homebrew8088/8088-PC-Compatible/Kicad/Other PCBs/ISA_BB/ISA_BB.kicad_pcb

## KiCad design Kicad/Other PCBs/ISA_BB/ISA_BB.kicad_pcb (2023-02-14)

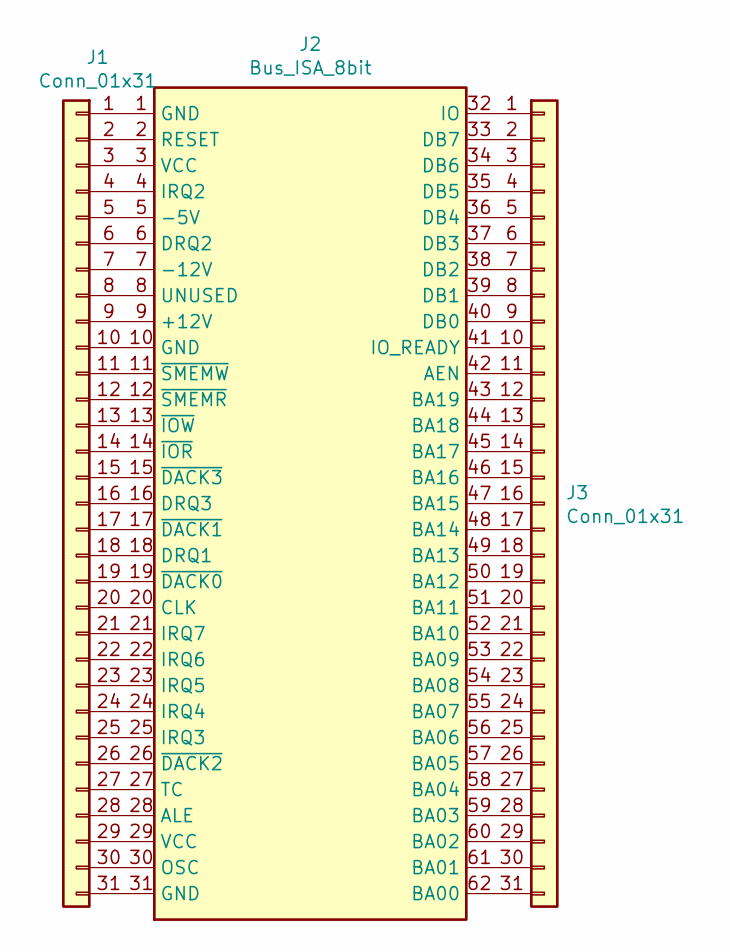
[picture p30: schematic ISA_BB.sch]

Parts:
J1, J3: Conn_01x31; PinHeader_1x31_P2.54mm_Vertical
J2: Bus_ISA_8bit; 8-bit-ISA

Connections:
unnamed: J1.1, J2.1 (GND)
unnamed: J1.2, J2.2 (RESET)
unnamed: J1.3, J2.3 (VCC)
unnamed: J1.4, J2.4 (IRQ2)
unnamed: J1.5, J2.5 (-5V)
unnamed: J1.6, J2.6 (DRQ2)
unnamed: J1.7, J2.7 (-12V)
unnamed: J1.8, J2.8 (UNUSED)
unnamed: J1.9, J2.9 (+12V)
unnamed: J1.10, J2.10 (GND)
unnamed: J1.11, J2.11 (~SMEMW)
unnamed: J1.12, J2.12 (~SMEMR)
unnamed: J1.13, J2.13 (~IOW)
unnamed: J1.14, J2.14 (~IOR)
unnamed: J1.15, J2.15 (~DACK3)
unnamed: J1.16, J2.16 (DRQ3)
unnamed: J1.17, J2.17 (~DACK1)
unnamed: J1.18, J2.18 (DRQ1)
unnamed: J1.19, J2.19 (~DACK0)
unnamed: J1.20, J2.20 (CLK)
unnamed: J1.21, J2.21 (IRQ7)
unnamed: J1.22, J2.22 (IRQ6)
unnamed: J1.23, J2.23 (IRQ5)
unnamed: J1.24, J2.24 (IRQ4)
unnamed: J1.25, J2.25 (IRQ3)
unnamed: J1.26, J2.26 (~DACK2)
unnamed: J1.27, J2.27 (TC)
unnamed: J1.28, J2.28 (ALE)
unnamed: J1.29, J2.29 (VCC)
unnamed: J1.30, J2.30 (OSC)
unnamed: J1.31, J2.31 (GND)
unnamed: J2.32 (IO), J3.1
unnamed: J2.33 (DB7), J3.2
unnamed: J2.34 (DB6), J3.3
unnamed: J2.35 (DB5), J3.4
unnamed: J2.36 (DB4), J3.5
unnamed: J2.37 (DB3), J3.6
unnamed: J2.38 (DB2), J3.7
unnamed: J2.39 (DB1), J3.8
unnamed: J2.40 (DB0), J3.9
unnamed: J2.41 (IO_READY), J3.10
unnamed: J2.42 (AEN), J3.11
unnamed: J2.43 (BA19), J3.12
unnamed: J2.44 (BA18), J3.13
unnamed: J2.45 (BA17), J3.14
unnamed: J2.46 (BA16), J3.15
unnamed: J2.47 (BA15), J3.16
unnamed: J2.48 (BA14), J3.17
unnamed: J2.49 (BA13), J3.18
unnamed: J2.50 (BA12), J3.19
unnamed: J2.51 (BA11), J3.20
unnamed: J2.52 (BA10), J3.21
unnamed: J2.53 (BA09), J3.22
unnamed: J2.54 (BA08), J3.23
unnamed: J2.55 (BA07), J3.24
unnamed: J2.56 (BA06), J3.25
unnamed: J2.57 (BA05), J3.26
unnamed: J2.58 (BA04), J3.27
unnamed: J2.59 (BA03), J3.28
unnamed: J2.60 (BA02), J3.29
unnamed: J2.61 (BA01), J3.30
unnamed: J2.62 (BA00), J3.31

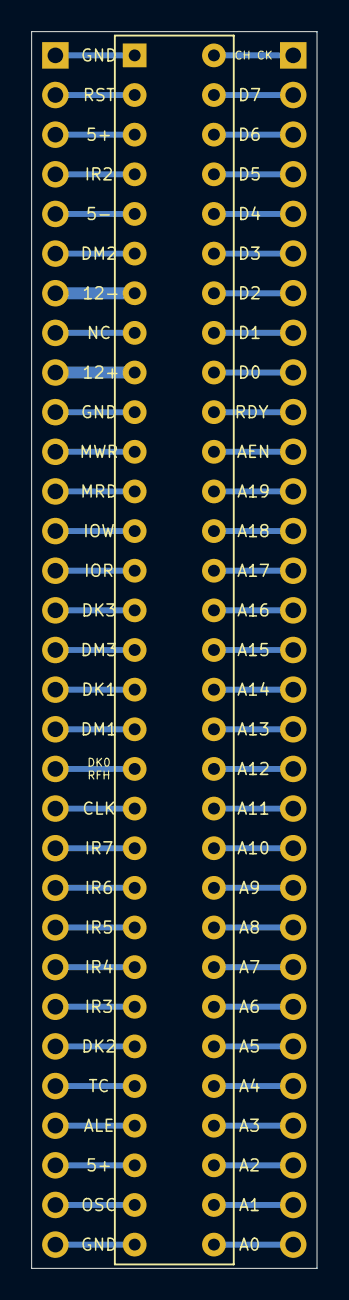
[picture p31: board ISA_BB.kicad_pcb from above]

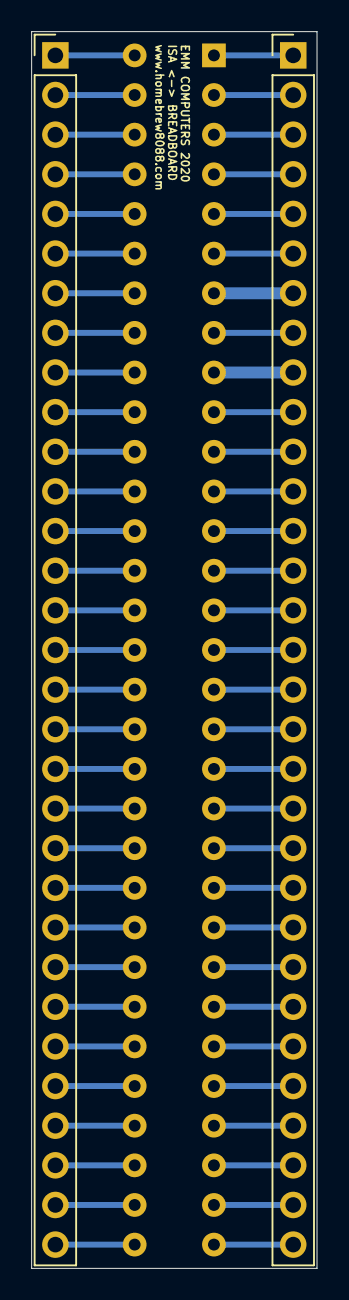
[picture p32: board ISA_BB.kicad_pcb from below]

Board: 2 copper layers, 18.3 x 79.2 mm, 3 parts (2 on the bottom side), 62 nets.
