homebrew8088/8088-PC-Compatible/Kicad/Other PCBs/512K ISA/512k.kicad_pcb

## KiCad design Kicad/Other PCBs/512K ISA/512k.kicad_pcb (2022-01-28)

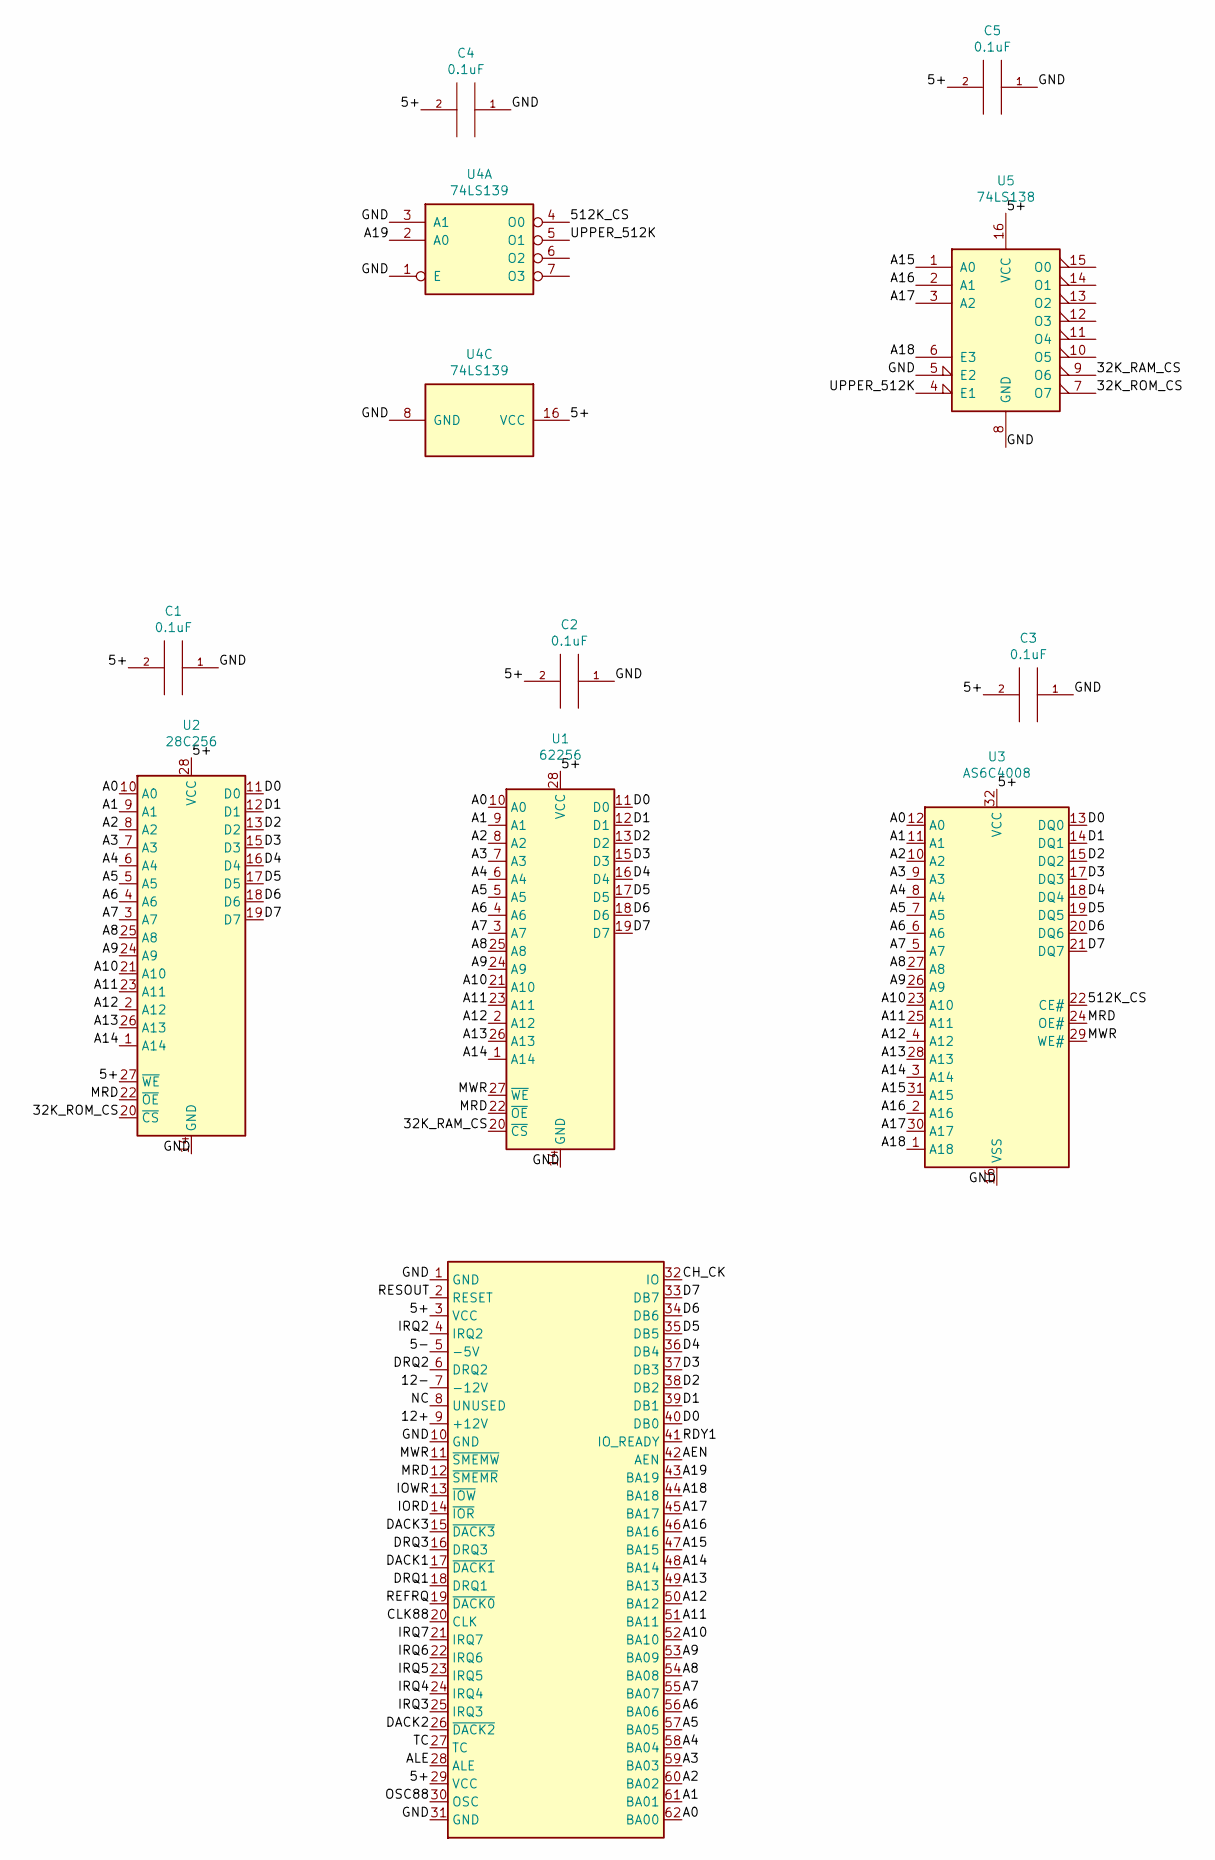
[picture p33: schematic 512k.sch]

Parts:
C1, C2, C3, C4, C5: 0.1uF; C_Disc_D4.3mm_W1.9mm_P5.00mm
J9: Bus_ISA_8bit; BUS_8_BIT
U1: 62256; DIP-28_W15.24mm
U2: 28C256; DIP_Socket-28_W11.9_W12.7_W15.24_W17.78_W18.5_3M_228-1277-0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
U3: AS6C4008; DIP-32_W15.24mm
U4: 74LS139; DIP-16_W7.62mm
U5: 74LS138; DIP-16_W7.62mm

Connections:
/5+: C1.2, C2.2, C3.2, C4.2, C5.2, J9.3 (VCC), J9.29 (VCC), U1.28 (VCC), U2.27 (~WE), U2.28 (VCC), U3.32 (VCC), U4.16 (VCC), U5.16 (VCC)
/5-: J9.5 (-5V)
/12+: J9.9 (+12V)
/12-: J9.7 (-12V)
/32K_RAM_CS: U1.20 (~CS), U5.9 (O6)
/32K_ROM_CS: U2.20 (~CS), U5.7 (O7)
/512K_CS: U3.22 (CE#), U4.4 (O0)
/A0: J9.62 (BA00), U1.10 (A0), U2.10 (A0), U3.12 (A0)
/A1: J9.61 (BA01), U1.9 (A1), U2.9 (A1), U3.11 (A1)
/A2: J9.60 (BA02), U1.8 (A2), U2.8 (A2), U3.10 (A2)
/A3: J9.59 (BA03), U1.7 (A3), U2.7 (A3), U3.9 (A3)
/A4: J9.58 (BA04), U1.6 (A4), U2.6 (A4), U3.8 (A4)
/A5: J9.57 (BA05), U1.5 (A5), U2.5 (A5), U3.7 (A5)
/A6: J9.56 (BA06), U1.4 (A6), U2.4 (A6), U3.6 (A6)
/A7: J9.55 (BA07), U1.3 (A7), U2.3 (A7), U3.5 (A7)
/A8: J9.54 (BA08), U1.25 (A8), U2.25 (A8), U3.27 (A8)
/A9: J9.53 (BA09), U1.24 (A9), U2.24 (A9), U3.26 (A9)
/A10: J9.52 (BA10), U1.21 (A10), U2.21 (A10), U3.23 (A10)
/A11: J9.51 (BA11), U1.23 (A11), U2.23 (A11), U3.25 (A11)
/A12: J9.50 (BA12), U1.2 (A12), U2.2 (A12), U3.4 (A12)
/A13: J9.49 (BA13), U1.26 (A13), U2.26 (A13), U3.28 (A13)
/A14: J9.48 (BA14), U1.1 (A14), U2.1 (A14), U3.3 (A14)
/A15: J9.47 (BA15), U3.31 (A15), U5.1 (A0)
/A16: J9.46 (BA16), U3.2 (A16), U5.2 (A1)
/A17: J9.45 (BA17), U3.30 (A17), U5.3 (A2)
/A18: J9.44 (BA18), U3.1 (A18), U5.6 (E3)
/A19: J9.43 (BA19), U4.2 (A0)
/AEN: J9.42 (AEN)
/ALE: J9.28 (ALE)
/CH_CK: J9.32 (IO)
/CLK88: J9.20 (CLK)
/D0: J9.40 (DB0), U1.11 (D0), U2.11 (D0), U3.13 (DQ0)
/D1: J9.39 (DB1), U1.12 (D1), U2.12 (D1), U3.14 (DQ1)
/D2: J9.38 (DB2), U1.13 (D2), U2.13 (D2), U3.15 (DQ2)
/D3: J9.37 (DB3), U1.15 (D3), U2.15 (D3), U3.17 (DQ3)
/D4: J9.36 (DB4), U1.16 (D4), U2.16 (D4), U3.18 (DQ4)
/D5: J9.35 (DB5), U1.17 (D5), U2.17 (D5), U3.19 (DQ5)
/D6: J9.34 (DB6), U1.18 (D6), U2.18 (D6), U3.20 (DQ6)
/D7: J9.33 (DB7), U1.19 (D7), U2.19 (D7), U3.21 (DQ7)
/DACK1: J9.17 (~DACK1)
/DACK2: J9.26 (~DACK2)
/DACK3: J9.15 (~DACK3)
/DRQ1: J9.18 (DRQ1)
/DRQ2: J9.6 (DRQ2)
/DRQ3: J9.16 (DRQ3)
/GND: C1.1, C2.1, C3.1, C4.1, C5.1, J9.1 (GND), J9.10 (GND), J9.31 (GND), U1.14 (GND), U2.14 (GND), U3.16 (VSS), U4.1 (E), U4.3 (A1), U4.8 (GND), U5.5 (E2), U5.8 (GND); also elsewhere on the board
/IORD: J9.14 (~IOR)
/IOWR: J9.13 (~IOW)
/IRQ2: J9.4 (IRQ2)
/IRQ3: J9.25 (IRQ3)
/IRQ4: J9.24 (IRQ4)
/IRQ5: J9.23 (IRQ5)
/IRQ6: J9.22 (IRQ6)
/IRQ7: J9.21 (IRQ7)
/MRD: J9.12 (~SMEMR), U1.22 (~OE), U2.22 (~OE), U3.24 (OE#)
/MWR: J9.11 (~SMEMW), U1.27 (~WE), U3.29 (WE#)
/NC: J9.8 (UNUSED)
/OSC88: J9.30 (OSC)
/RDY1: J9.41 (IO_READY)
/REFRQ: J9.19 (~DACK0)
/RESOUT: J9.2 (RESET)
/TC: J9.27 (TC)
/UPPER_512K: U4.5 (O1), U5.4 (E1)

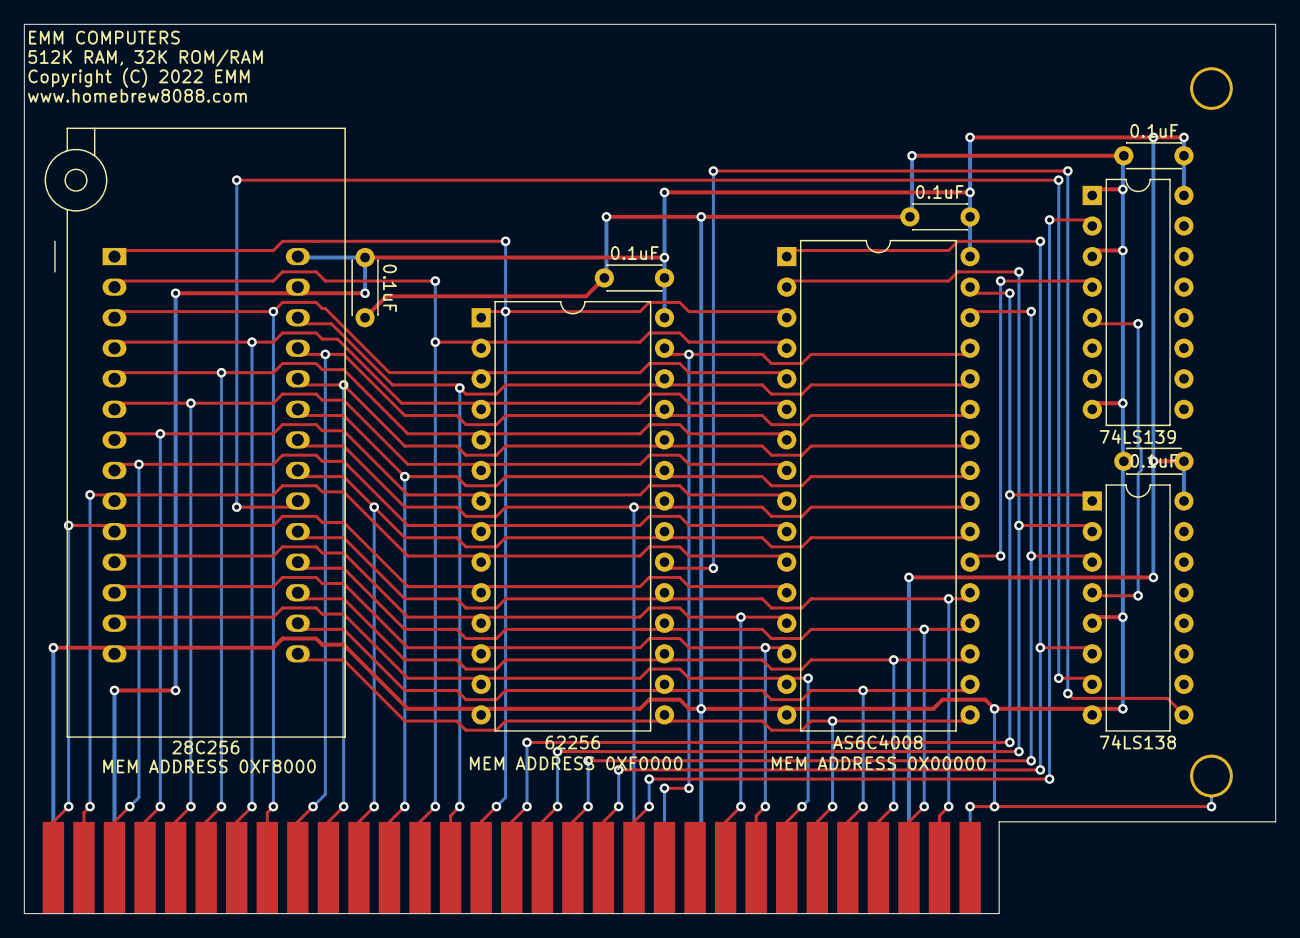
[picture p34: board 512k.kicad_pcb from above]

Board: 2 copper layers, 104.0 x 73.9 mm, 13 parts (0 on the bottom side), 36 nets.

Other parts of the board:
R: L; Large_Via
R#2: L; Large_Via

Their connections:
/GND: R.1; also elsewhere on the board
