homebrew8088/8088-PC-Compatible/Kicad/Other PCBs/LCD 8255/LCD 8255.kicad_pcb

## KiCad design Kicad/Other PCBs/LCD 8255/LCD 8255.kicad_pcb (2022-04-25)

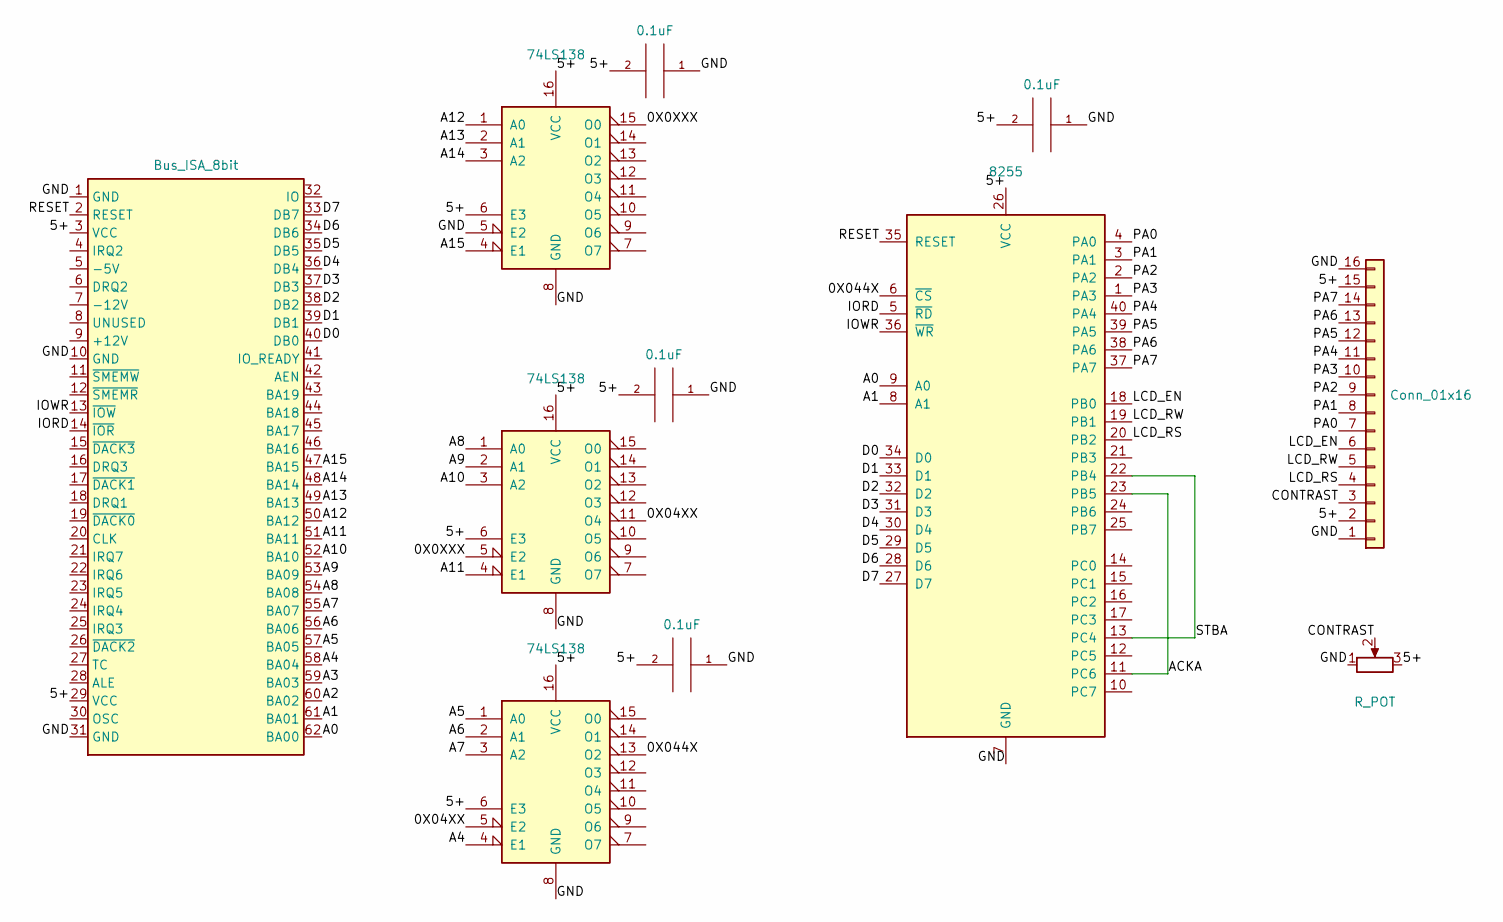
[picture p35: schematic LCD 8255.sch]

Parts:
C1, C2, C3, C4: 0.1uF; C_Disc_D4.3mm_W1.9mm_P5.00mm
J1: Bus_ISA_8bit; BUS_8_BIT
J2: Conn_01x16; PinHeader_1x16_P2.54mm_Vertical
RV1: R_POT; Potentiometer_Piher_PT-6-V_Vertical
U1, U2, U3: 74LS138; DIP-16_W7.62mm
U4: 8255; DIP-40_W15.24mm

Connections:
/0X0XXX: U1.15 (O0), U2.5 (E2)
/0X04XX: U2.11 (O4), U3.5 (E2)
/0X044X: U3.13 (O2), U4.6 (~CS~)
/5+: C1.2, C2.2, C3.2, C4.2, J1.3 (VCC), J1.29 (VCC), J2.2, J2.15, RV1.3, U1.6 (E3), U1.16 (VCC), U2.6 (E3), U2.16 (VCC), U3.6 (E3), U3.16 (VCC), U4.26 (VCC)
/A0: J1.62 (BA00), U4.9 (A0)
/A1: J1.61 (BA01), U4.8 (A1)
/A2: J1.60 (BA02)
/A3: J1.59 (BA03)
/A4: J1.58 (BA04), U3.4 (E1)
/A5: J1.57 (BA05), U3.1 (A0)
/A6: J1.56 (BA06), U3.2 (A1)
/A7: J1.55 (BA07), U3.3 (A2)
/A8: J1.54 (BA08), U2.1 (A0)
/A9: J1.53 (BA09), U2.2 (A1)
/A10: J1.52 (BA10), U2.3 (A2)
/A11: J1.51 (BA11), U2.4 (E1)
/A12: J1.50 (BA12), U1.1 (A0)
/A13: J1.49 (BA13), U1.2 (A1)
/A14: J1.48 (BA14), U1.3 (A2)
/A15: J1.47 (BA15), U1.4 (E1)
/ACKA: U4.11 (PC6), U4.23 (PB5)
/CONTRAST: J2.3, RV1.2
/D0: J1.40 (DB0), U4.34 (D0)
/D1: J1.39 (DB1), U4.33 (D1)
/D2: J1.38 (DB2), U4.32 (D2)
/D3: J1.37 (DB3), U4.31 (D3)
/D4: J1.36 (DB4), U4.30 (D4)
/D5: J1.35 (DB5), U4.29 (D5)
/D6: J1.34 (DB6), U4.28 (D6)
/D7: J1.33 (DB7), U4.27 (D7)
/GND: C1.1, C2.1, C3.1, C4.1, J1.1 (GND), J1.10 (GND), J1.31 (GND), J2.1, J2.16, RV1.1, U1.5 (E2), U1.8 (GND), U2.8 (GND), U3.8 (GND), U4.7 (GND); also elsewhere on the board
/IORD: J1.14 (~IOR), U4.5 (~RD~)
/IOWR: J1.13 (~IOW), U4.36 (~WR~)
/LCD_EN: J2.6, U4.18 (PB0)
/LCD_RS: J2.4, U4.20 (PB2)
/LCD_RW: J2.5, U4.19 (PB1)
/PA0: J2.7, U4.4 (PA0)
/PA1: J2.8, U4.3 (PA1)
/PA2: J2.9, U4.2 (PA2)
/PA3: J2.10, U4.1 (PA3)
/PA4: J2.11, U4.40 (PA4)
/PA5: J2.12, U4.39 (PA5)
/PA6: J2.13, U4.38 (PA6)
/PA7: J2.14, U4.37 (PA7)
/RESET: J1.2 (RESET), U4.35 (RESET)
/STBA: U4.13 (PC4), U4.22 (PB4)

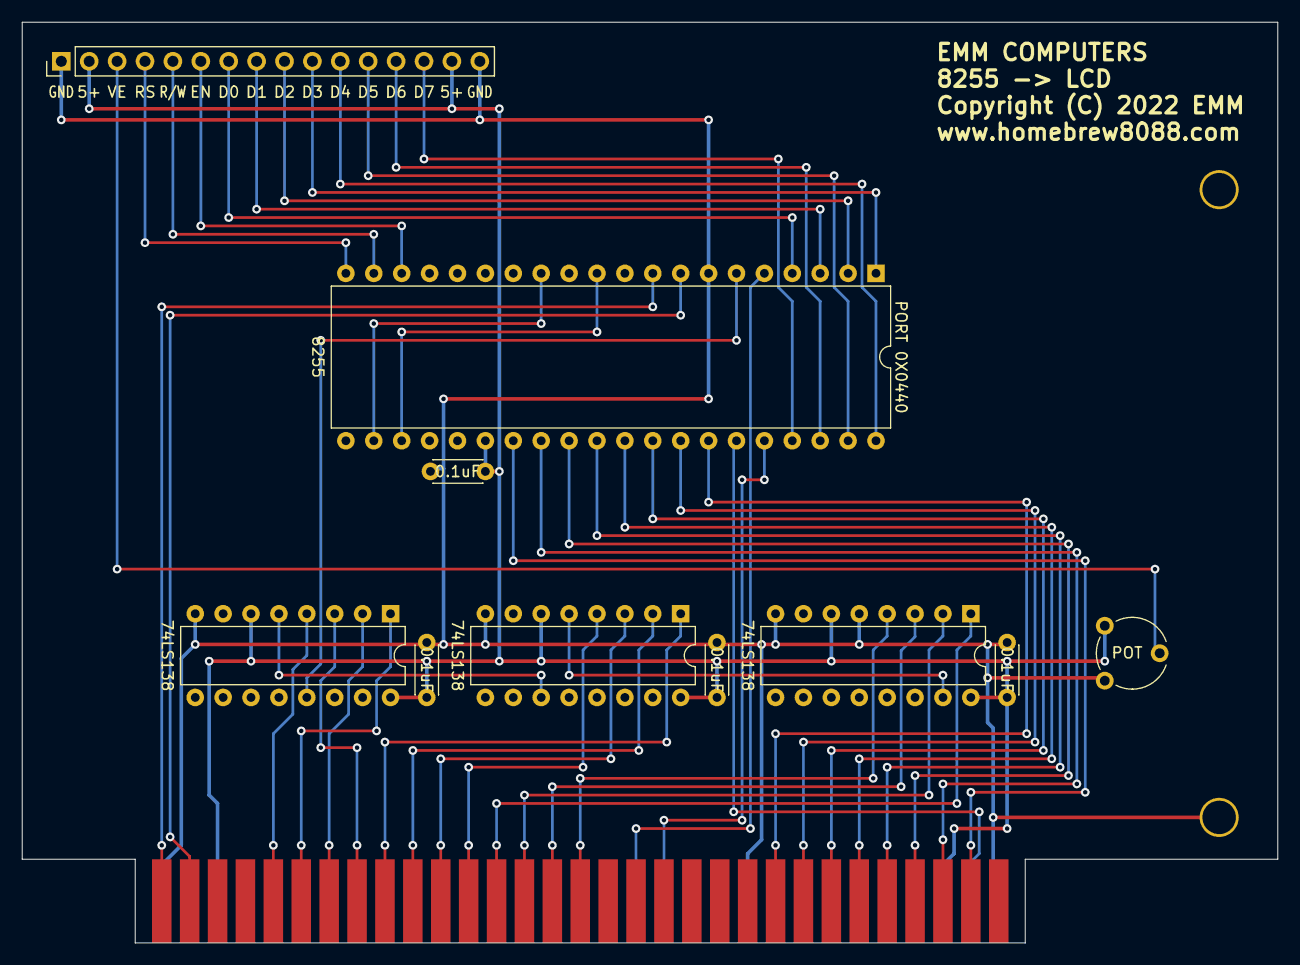
[picture p36: board LCD 8255.kicad_pcb from above]

Board: 2 copper layers, 114.3 x 83.8 mm, 13 parts (0 on the bottom side), 44 nets.

Other parts of the board:
R: L; Large_Via
R#2: L; Large_Via

Their connections:
/GND: R.1; also elsewhere on the board
