homebrew8088/8088-PC-Compatible/Kicad/V40 64K 640K ISA/V40 64K 640K ISA.kicad_pcb

## KiCad design Kicad/V40 64K 640K ISA/V40 64K 640K ISA.kicad_pcb (2023-02-17)

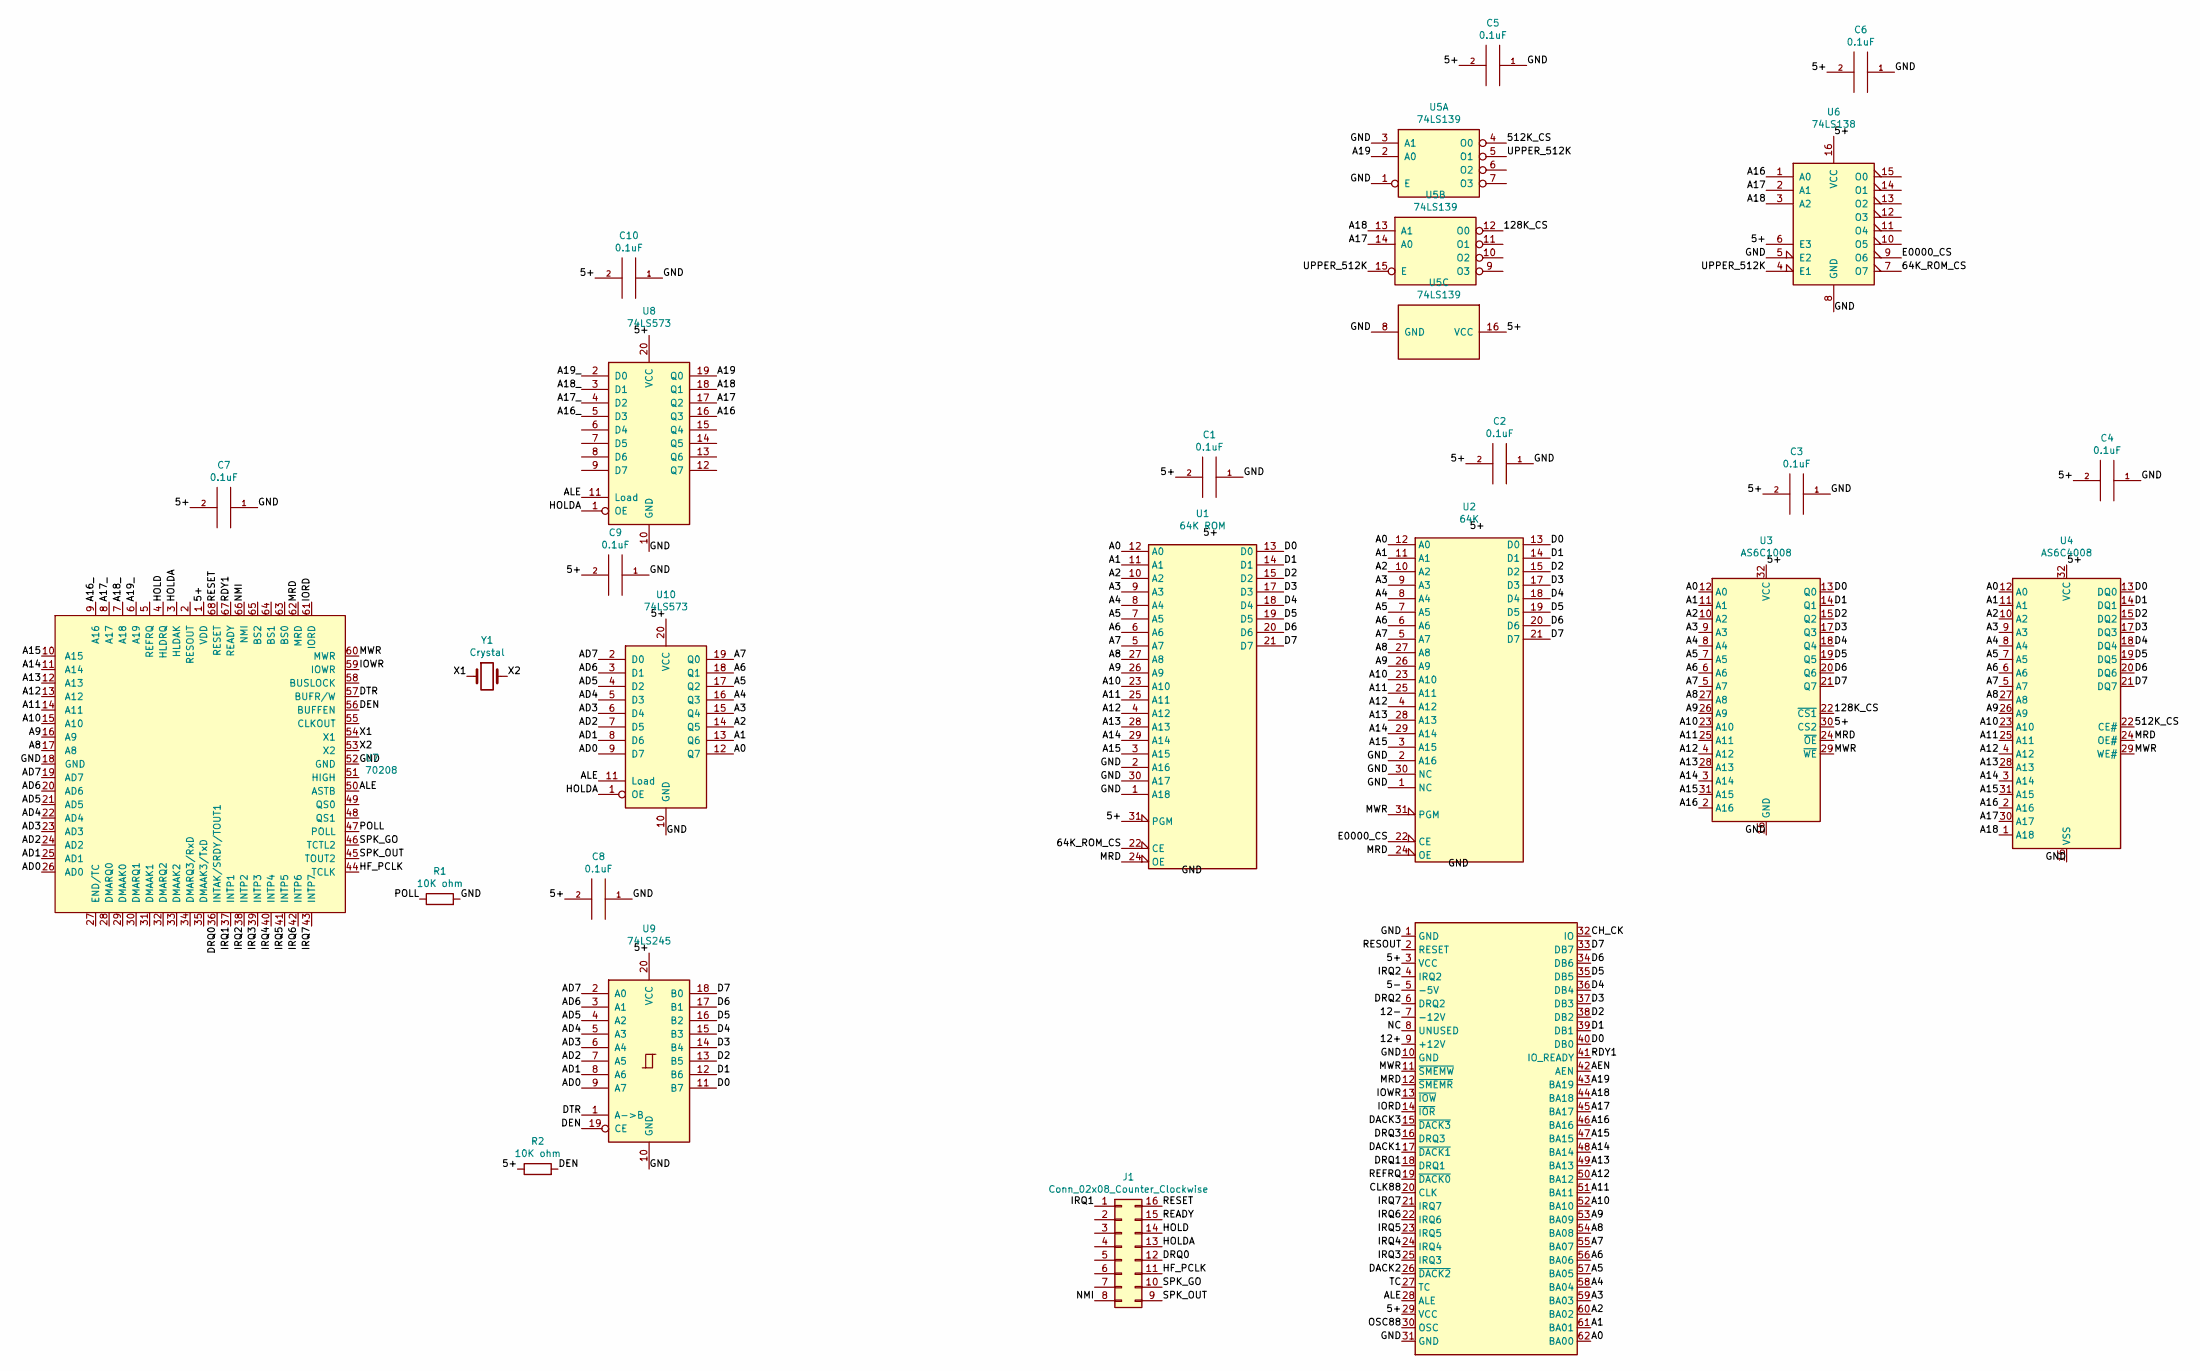
[picture p37: schematic V40 64K 640K ISA.sch]

Parts:
C1, C2, C3, C4, C5, C6, C7, C8, C9, C10: 0.1uF; C_Disc_D4.3mm_W1.9mm_P5.00mm
J1: Conn_02x08_Counter_Clockwise; 16_EDGE_CARD_BUS
J9: Bus_ISA_8bit; BUS_8_BIT
R1, R2: 10K ohm; R_Axial_DIN0207_L6.3mm_D2.5mm_P10.16mm_Horizontal
U1: 64K ROM; DIP_Socket-32_W11.9_W12.7_W15.24_W17.78_W18.5_3M_232-1285-0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
U2: 64K; DIP-32_W15.24mm
U3: AS6C1008; DIP-32_W15.24mm
U4: AS6C4008; DIP-32_W15.24mm
U5: 74LS139; DIP-16_W7.62mm
U6: 74LS138; DIP-16_W7.62mm
U7: 70208; PLCC-68_THT-Socket
U8, U10: 74LS573; DIP-20_W7.62mm
U9: 74LS245; DIP-20_W7.62mm
Y1: Crystal; Crystal_HC18-U_Vertical

Connections:
/5-: J9.5 (-5V)
/12+: J9.9 (+12V)
/12-: J9.7 (-12V)
/64K_ROM_CS: U1.22 (CE), U6.7 (O7)
/128K_CS: U3.22 (~CS1), U5.12 (O0)
/512K_CS: U4.22 (CE#), U5.4 (O0)
/A0: J9.62 (BA00), U1.12 (A0), U2.12 (A0), U3.12 (A0), U4.12 (A0), U10.12 (Q7)
/A1: J9.61 (BA01), U1.11 (A1), U2.11 (A1), U3.11 (A1), U4.11 (A1), U10.13 (Q6)
/A2: J9.60 (BA02), U1.10 (A2), U2.10 (A2), U3.10 (A2), U4.10 (A2), U10.14 (Q5)
/A3: J9.59 (BA03), U1.9 (A3), U2.9 (A3), U3.9 (A3), U4.9 (A3), U10.15 (Q4)
/A4: J9.58 (BA04), U1.8 (A4), U2.8 (A4), U3.8 (A4), U4.8 (A4), U10.16 (Q3)
/A5: J9.57 (BA05), U1.7 (A5), U2.7 (A5), U3.7 (A5), U4.7 (A5), U10.17 (Q2)
/A6: J9.56 (BA06), U1.6 (A6), U2.6 (A6), U3.6 (A6), U4.6 (A6), U10.18 (Q1)
/A7: J9.55 (BA07), U1.5 (A7), U2.5 (A7), U3.5 (A7), U4.5 (A7), U10.19 (Q0)
/A8: J9.54 (BA08), U1.27 (A8), U2.27 (A8), U3.27 (A8), U4.27 (A8), U7.17 (A8)
/A9: J9.53 (BA09), U1.26 (A9), U2.26 (A9), U3.26 (A9), U4.26 (A9), U7.16 (A9)
/A10: J9.52 (BA10), U1.23 (A10), U2.23 (A10), U3.23 (A10), U4.23 (A10), U7.15 (A10)
/A11: J9.51 (BA11), U1.25 (A11), U2.25 (A11), U3.25 (A11), U4.25 (A11), U7.14 (A11)
/A12: J9.50 (BA12), U1.4 (A12), U2.4 (A12), U3.4 (A12), U4.4 (A12), U7.13 (A12)
/A13: J9.49 (BA13), U1.28 (A13), U2.28 (A13), U3.28 (A13), U4.28 (A13), U7.12 (A13)
/A14: J9.48 (BA14), U1.29 (A14), U2.29 (A14), U3.3 (A14), U4.3 (A14), U7.11 (A14)
/A15: J9.47 (BA15), U1.3 (A15), U2.3 (A15), U3.31 (A15), U4.31 (A15), U7.10 (A15)
/A16: J9.46 (BA16), U3.2 (A16), U4.2 (A16), U6.1 (A0), U8.16 (Q3)
/A16_: U7.9 (A16), U8.5 (D3)
/A17: J9.45 (BA17), U4.30 (A17), U5.14 (A0), U6.2 (A1), U8.17 (Q2)
/A17_: U7.8 (A17), U8.4 (D2)
/A18: J9.44 (BA18), U4.1 (A18), U5.13 (A1), U6.3 (A2), U8.18 (Q1)
/A18_: U7.7 (A18), U8.3 (D1)
/A19: J9.43 (BA19), U5.2 (A0), U8.19 (Q0)
/A19_: U7.6 (A19), U8.2 (D0)
/AD0: U7.26 (AD0), U9.9 (A7), U10.9 (D7)
/AD1: U7.25 (AD1), U9.8 (A6), U10.8 (D6)
/AD2: U7.24 (AD2), U9.7 (A5), U10.7 (D5)
/AD3: U7.23 (AD3), U9.6 (A4), U10.6 (D4)
/AD4: U7.22 (AD4), U9.5 (A3), U10.5 (D3)
/AD5: U7.21 (AD5), U9.4 (A2), U10.4 (D2)
/AD6: U7.20 (AD6), U9.3 (A1), U10.3 (D1)
/AD7: U7.19 (AD7), U9.2 (A0), U10.2 (D0)
/AEN: J9.42 (AEN)
/ALE: J9.28 (ALE), U7.50 (ASTB), U8.11 (Load), U10.11 (Load)
/CH_CK: J9.32 (IO)
/CLK88: J9.20 (CLK)
/D0: J9.40 (DB0), U1.13 (D0), U2.13 (D0), U3.13 (Q0), U4.13 (DQ0), U9.11 (B7)
/D1: J9.39 (DB1), U1.14 (D1), U2.14 (D1), U3.14 (Q1), U4.14 (DQ1), U9.12 (B6)
/D2: J9.38 (DB2), U1.15 (D2), U2.15 (D2), U3.15 (Q2), U4.15 (DQ2), U9.13 (B5)
/D3: J9.37 (DB3), U1.17 (D3), U2.17 (D3), U3.17 (Q3), U4.17 (DQ3), U9.14 (B4)
/D4: J9.36 (DB4), U1.18 (D4), U2.18 (D4), U3.18 (Q4), U4.18 (DQ4), U9.15 (B3)
/D5: J9.35 (DB5), U1.19 (D5), U2.19 (D5), U3.19 (Q5), U4.19 (DQ5), U9.16 (B2)
/D6: J9.34 (DB6), U1.20 (D6), U2.20 (D6), U3.20 (Q6), U4.20 (DQ6), U9.17 (B1)
/D7: J9.33 (DB7), U1.21 (D7), U2.21 (D7), U3.21 (Q7), U4.21 (DQ7), U9.18 (B0)
/DACK1: J9.17 (~DACK1)
/DACK2: J9.26 (~DACK2)
/DACK3: J9.15 (~DACK3)
/DEN: R2.2, U7.56 (BUFFEN), U9.19 (CE)
/DRQ0: J1.12, U7.36 (INTAK/SRDY/TOUT1)
/DRQ1: J9.18 (DRQ1)
/DRQ2: J9.6 (DRQ2)
/DRQ3: J9.16 (DRQ3)
/DTR: U7.57 (BUFR/W), U9.1 (A->B)
/E0000_CS: U2.22 (CE), U6.9 (O6)
/HF_PCLK: J1.11, U7.44 (TCLK)
/HOLD: J1.14, U7.4 (HLDRQ)
/HOLDA: J1.13, U7.3 (HLDAK), U8.1 (OE), U10.1 (OE)
/IORD: J9.14 (~IOR), U7.61 (IORD)
/IOWR: J9.13 (~IOW), U7.59 (IOWR)
/IRQ1: J1.1, U7.37 (INTP1)
/IRQ2: J9.4 (IRQ2), U7.38 (INTP2)
/IRQ3: J9.25 (IRQ3), U7.39 (INTP3)
/IRQ4: J9.24 (IRQ4), U7.40 (INTP4)
/IRQ5: J9.23 (IRQ5), U7.41 (INTP5)
/IRQ6: J9.22 (IRQ6), U7.42 (INTP6)
/IRQ7: J9.21 (IRQ7), U7.43 (INTP7)
/MRD: J9.12 (~SMEMR), U1.24 (OE), U2.24 (OE), U3.24 (~OE), U4.24 (OE#), U7.62 (MRD)
/MWR: J9.11 (~SMEMW), U2.31 (PGM), U3.29 (~WE), U4.29 (WE#), U7.60 (MWR)
/NC: J9.8 (UNUSED)
/NMI: J1.8, U7.66 (NMI)
/OSC88: J9.30 (OSC)
/POLL: R1.1, U7.47 (POLL)
/RDY1: J9.41 (IO_READY), U7.67 (READY)
/READY: J1.15
/REFRQ: J9.19 (~DACK0)
/RESET: J1.16, U7.68 (RESET)
/RESOUT: J9.2 (RESET)
/SPK_GO: J1.10, U7.46 (TCTL2)
/SPK_OUT: J1.9, U7.45 (TOUT2)
/TC: J9.27 (TC)
/UPPER_512K: U5.5 (O1), U5.15 (E), U6.4 (E1)
/X1: U7.54 (X1), Y1.1
/X2: U7.53 (X2), Y1.2
GND: C1.1, C2.1, C3.1, C4.1, C5.1, C6.1, C7.1, C8.1, C9.1, C10.1, J9.1 (GND), J9.10 (GND), J9.31 (GND), R1.2, U1.1 (A18), U1.2 (A16), U1.16 (GND), U1.30 (A17), U2.1 (NC), U2.2 (A16), U2.16 (GND), U2.30 (NC), U3.16 (GND), U4.16 (VSS), U5.1 (E), U5.3 (A1), U5.8 (GND), U6.5 (E2), U6.8 (GND), U7.18 (GND), U7.52 (GND), U8.10 (GND), U9.10 (GND), U10.10 (GND); also elsewhere on the board
VCC: C1.2, C2.2, C3.2, C4.2, C5.2, C6.2, C7.2, C8.2, C9.2, C10.2, J9.3 (VCC), J9.29 (VCC), R2.1, U1.31 (PGM), U1.32 (VCC), U2.32 (VCC), U3.30 (CS2), U3.32 (VCC), U4.32 (VCC), U5.16 (VCC), U6.6 (E3), U6.16 (VCC), U7.1 (VDD), U8.20 (VCC), U9.20 (VCC), U10.20 (VCC)

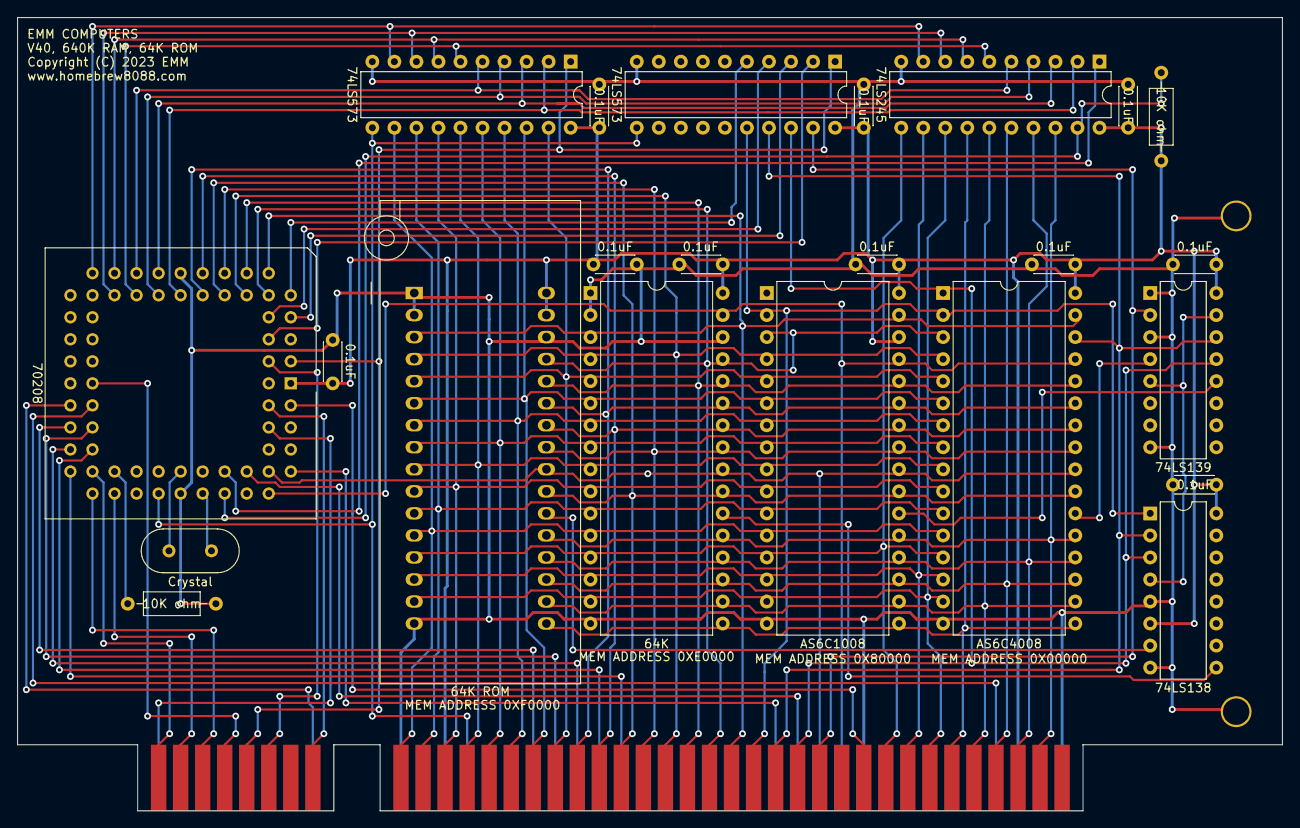
[picture p38: board V40 64K 640K ISA.kicad_pcb from above]

Board: 2 copper layers, 145.8 x 91.4 mm, 27 parts (0 on the bottom side), 73 nets.

Other parts of the board:
R: L; Large_Via
R#2: L; Large_Via

Their connections:
GND: R.1, R#2.1; also elsewhere on the board
